HeinrichG-V12/HFM_Adapter/hardware/Housing/002.jpg

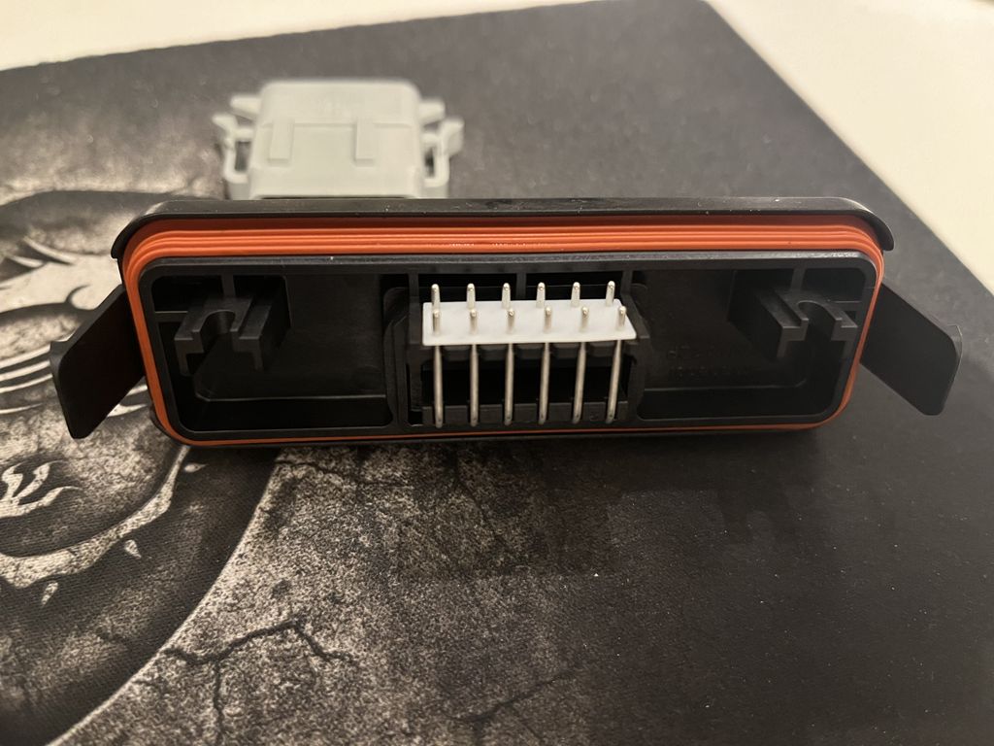
hardware/Housing/002.jpg
